impatrq/smart_toolbox/circuitos/cIrcuito-impreso/imagenes/PCB-vista-inferior.png

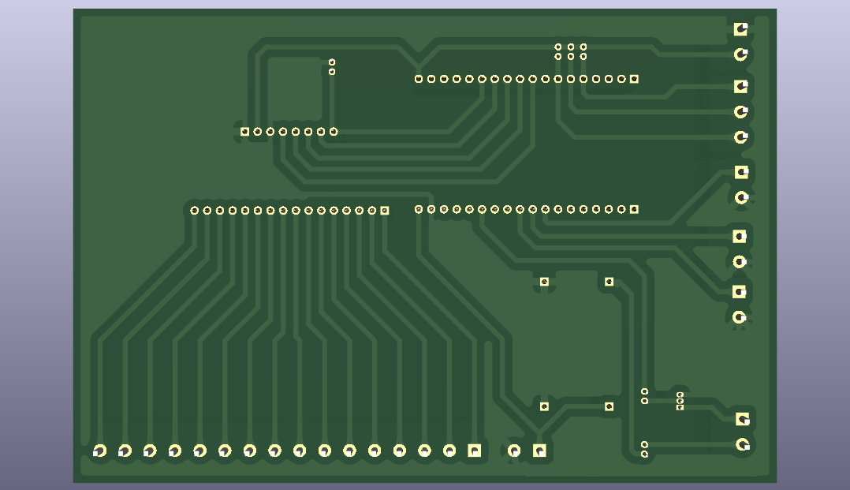
circuitos/cIrcuito-impreso/imagenes/PCB-vista-inferior.png
