impatrq/smart_toolbox/circuitos/cIrcuito-impreso/imagenes/PCB.png

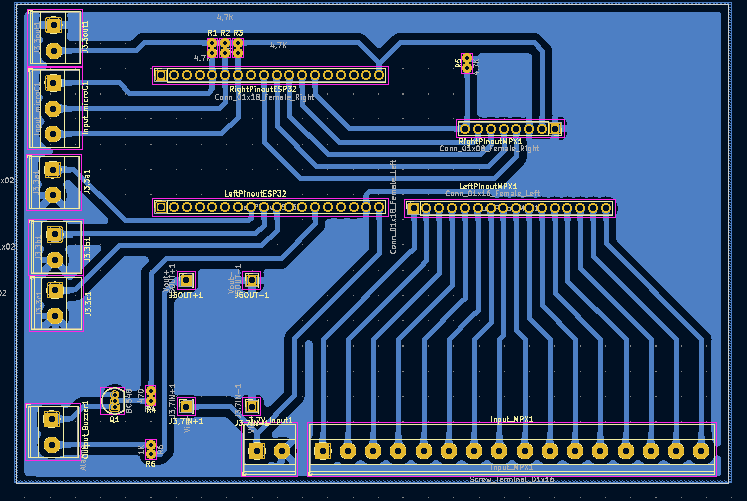
circuitos/cIrcuito-impreso/imagenes/PCB.png
