impatrq/smart_toolbox/circuitos/placa-de-control/imagenes/placa_de_control.jpg

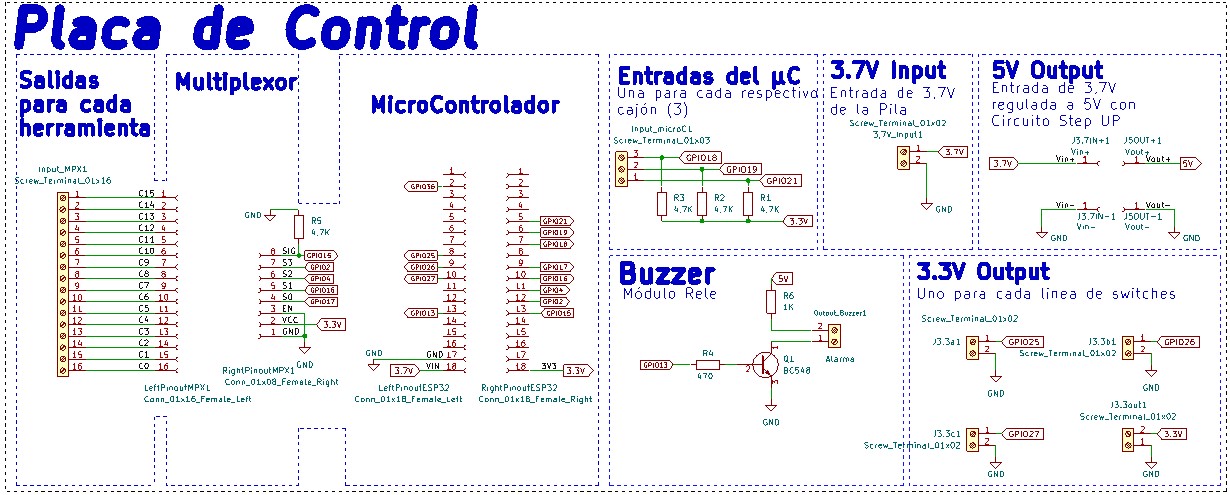
circuitos/placa-de-control/imagenes/placa_de_control.jpg
